CENTRALINOproject/CENTRALINO_BETA/Design/Software/Arduino_sketches/Graphic_&_Oled/coordinate-grid-graph-paper_238032.jpg

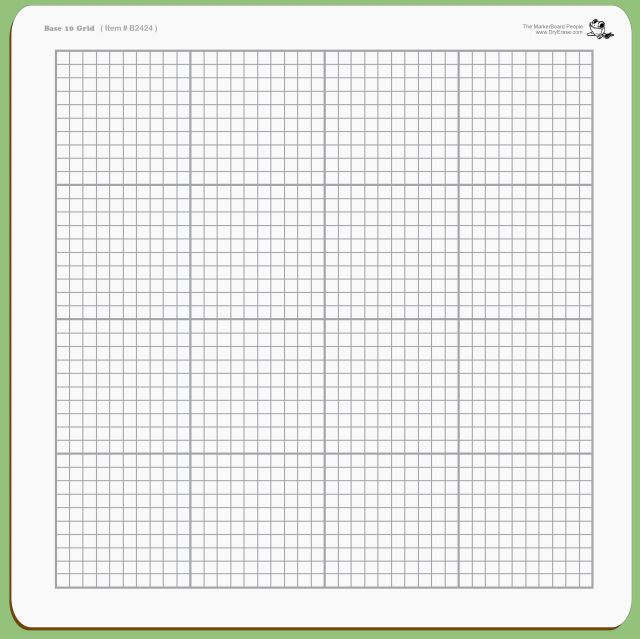
Design/Software/Arduino_sketches/Graphic_&_Oled/coordinate-grid-graph-paper_238032.jpg
