CENTRALINOproject/CENTRALINO_BETA/Design/Software/Arduino_sketches/Graphic_&_Oled/DIYmall-0-96-Inch-Yellow-and-Blue-I2C-IIC-OLED-LCD-Module-Serial-128X64-Display-for.jpg

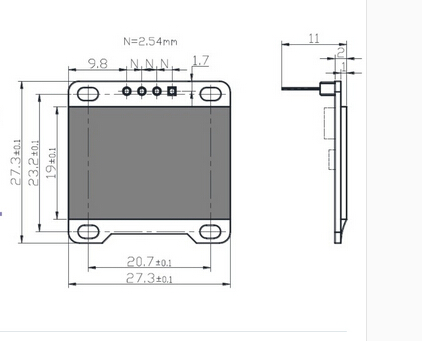
Design/Software/Arduino_sketches/Graphic_&_Oled/DIYmall-0-96-Inch-Yellow-and-Blue-I2C-IIC-OLED-LCD-Module-Serial-128X64-Display-for.jpg
