CENTRALINOproject/CENTRALINO_BETA/Information_Gathering/Multimedia/bluetooth_pinout/HC-05-FC-114-HC-06-FC-114-Connections-to-Arduino.jpg

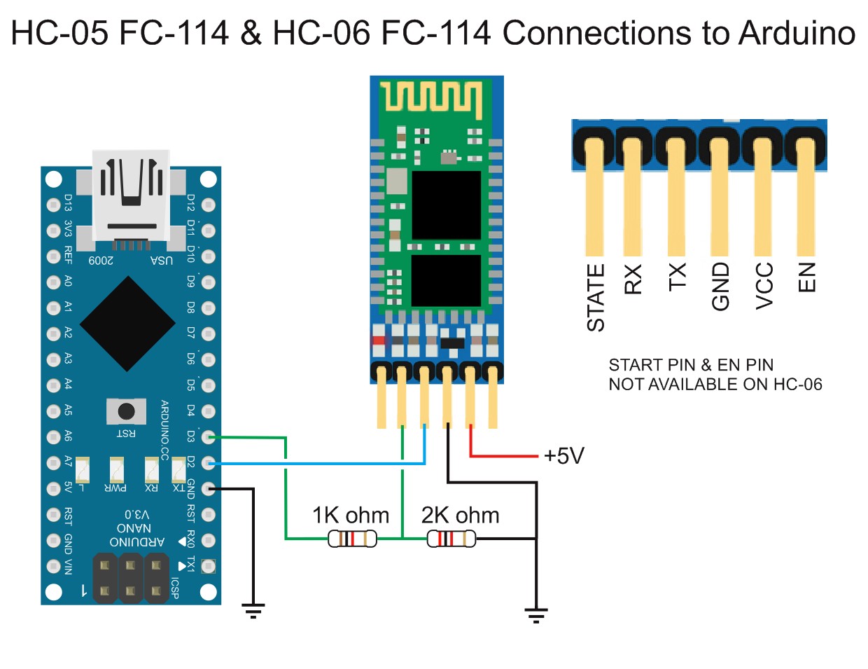
Information_Gathering/Multimedia/bluetooth_pinout/HC-05-FC-114-HC-06-FC-114-Connections-to-Arduino.jpg
