CENTRALINOproject/CENTRALINO_BETA/Information_Gathering/Multimedia/calcolo_per_resistenza.jpg

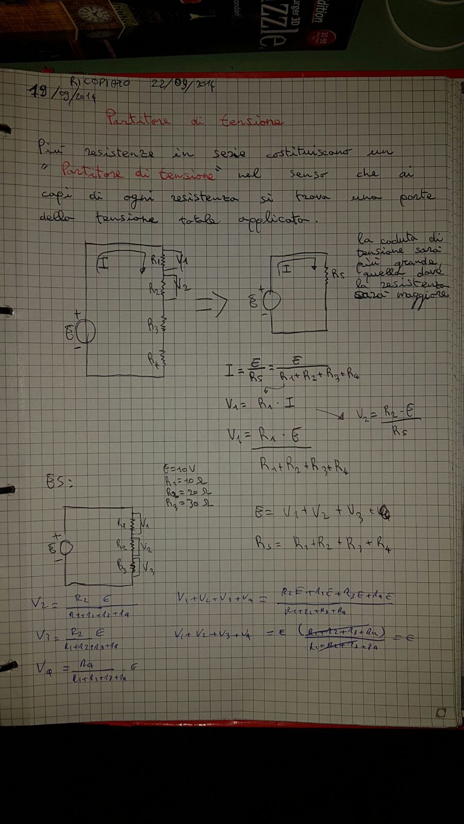
Information_Gathering/Multimedia/calcolo_per_resistenza.jpg
