CENTRALINOproject/CENTRALINO_BETA/Information_Gathering/Multimedia/hc_05_06_multimedia/bluetooth hc05.png

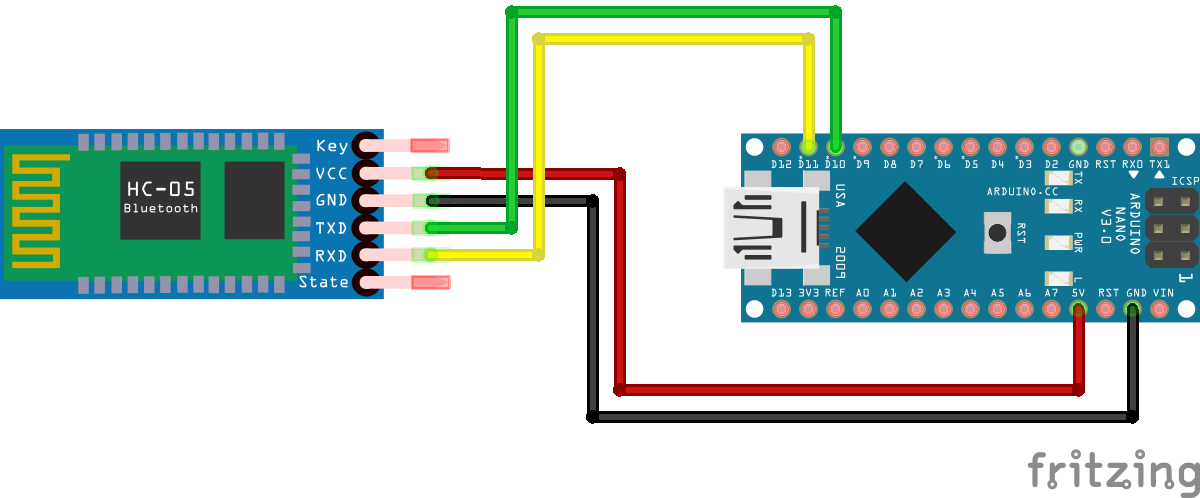
Information_Gathering/Multimedia/hc_05_06_multimedia/bluetooth hc05.png
