CENTRALINOproject/CENTRALINO_BETA/Information_Gathering/Multimedia/hc_05_06_multimedia/hc06_arduino.jpg

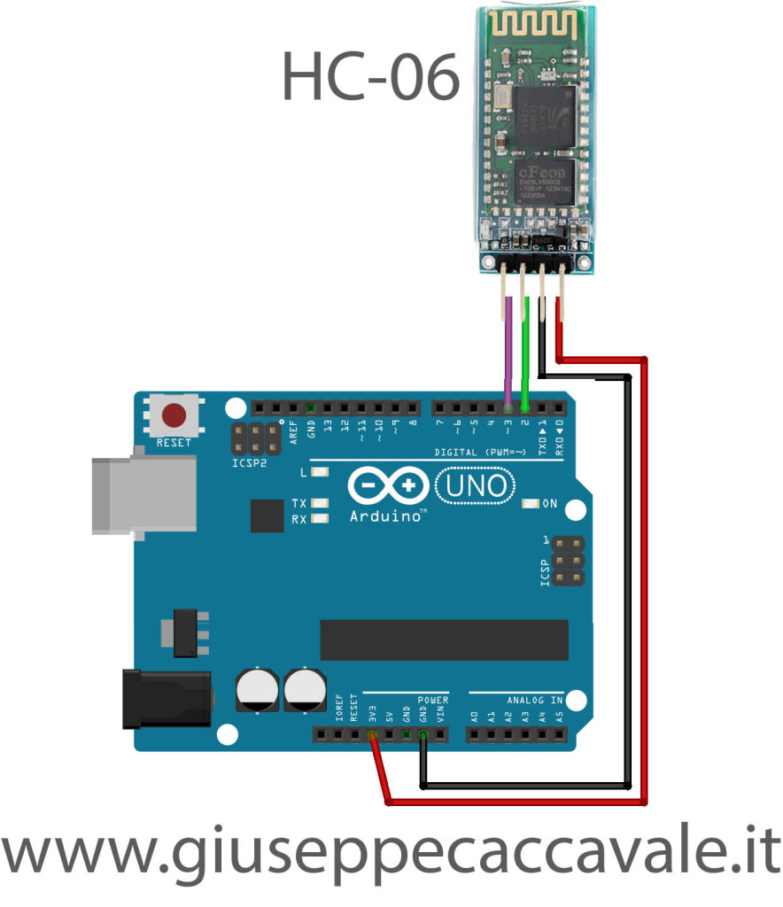
Information_Gathering/Multimedia/hc_05_06_multimedia/hc06_arduino.jpg
