CENTRALINOproject/CENTRALINO_BETA/Information_Gathering/Multimedia/Ir_pinout/ir_receiver_sender_bb.png

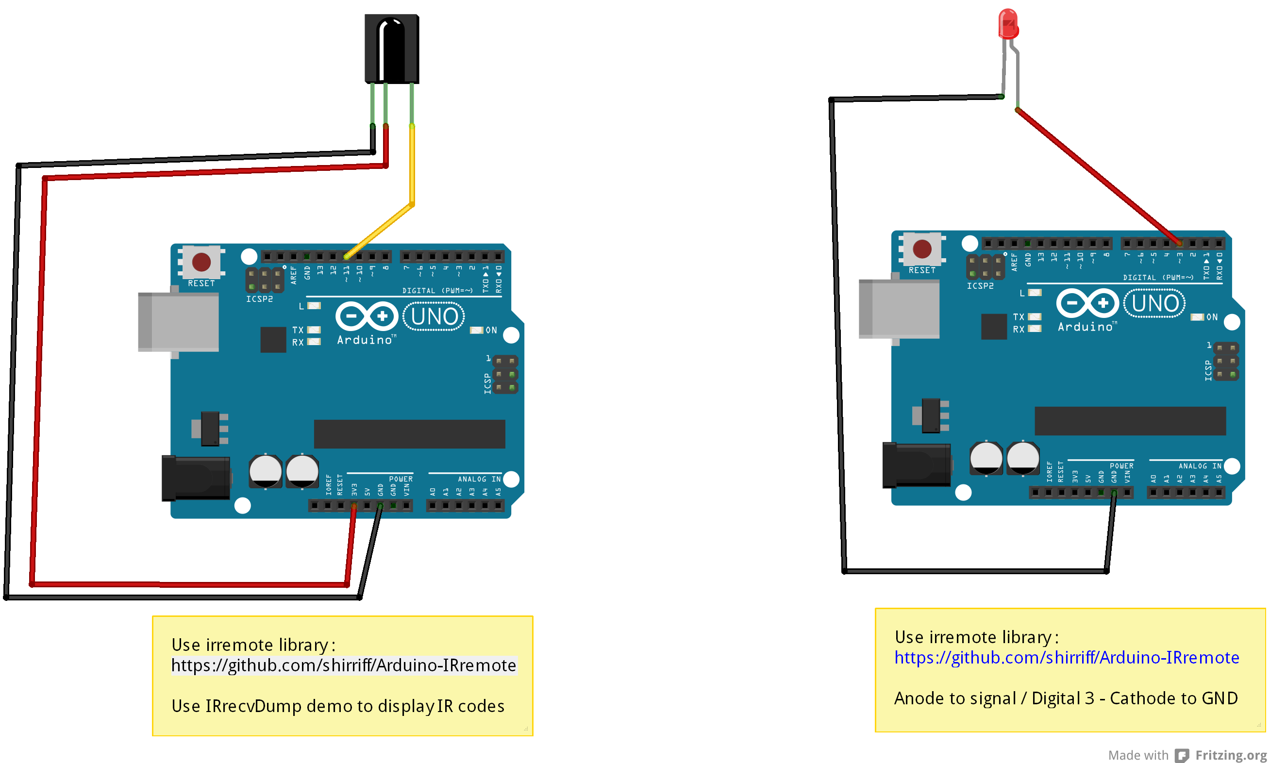
Information_Gathering/Multimedia/Ir_pinout/ir_receiver_sender_bb.png
