CENTRALINOproject/CENTRALINO_BETA/Information_Gathering/Multimedia/mpu6050_multimedia/IMAG0190.jpg

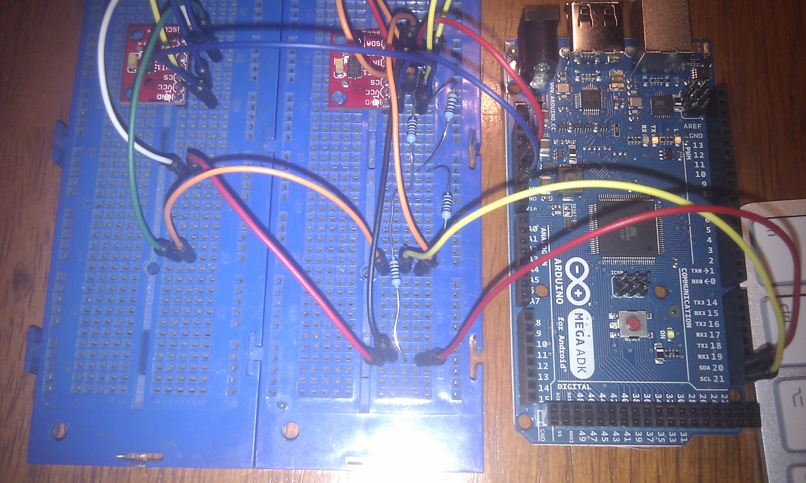
Information_Gathering/Multimedia/mpu6050_multimedia/IMAG0190.jpg
