CENTRALINOproject/CENTRALINO_BETA/Information_Gathering/Multimedia/mpu6050_multimedia/Immagine2.png

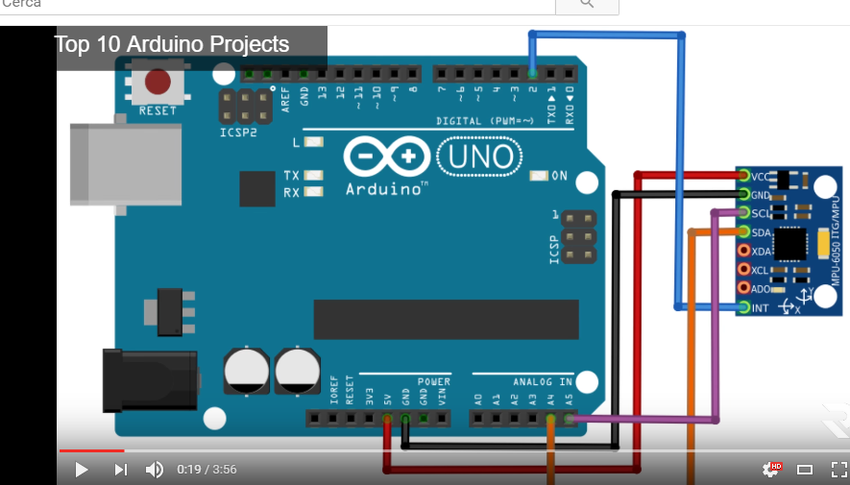
Information_Gathering/Multimedia/mpu6050_multimedia/Immagine2.png
