CENTRALINOproject/CENTRALINO_BETA/Information_Gathering/Multimedia/mpu6050_multimedia/MPU 506 connectivity.jpg

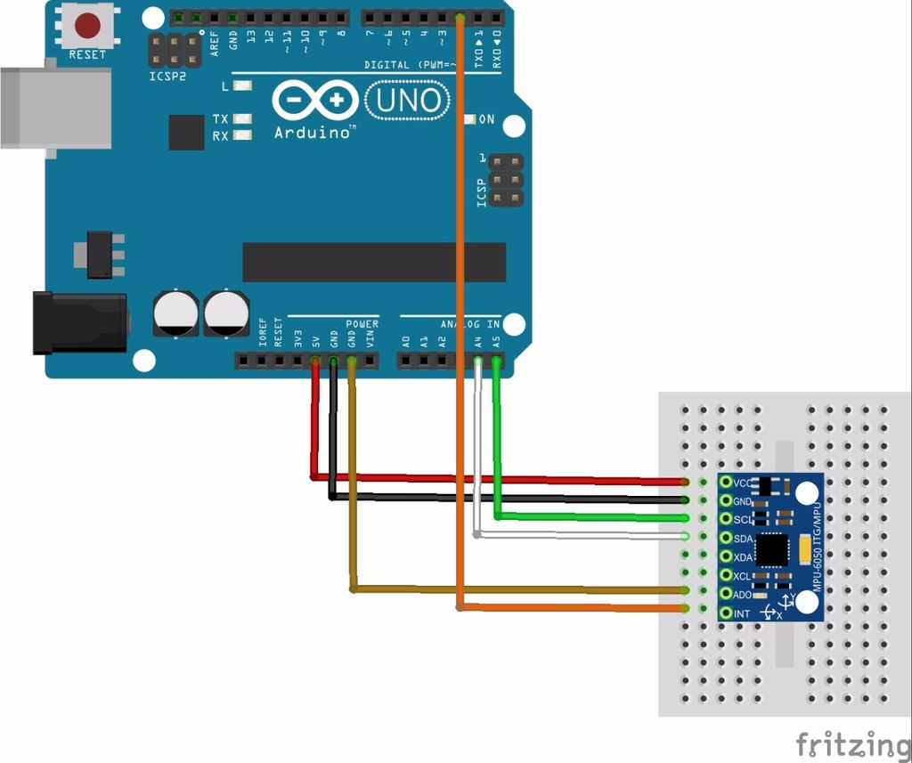
Information_Gathering/Multimedia/mpu6050_multimedia/MPU 506 connectivity.jpg
