CENTRALINOproject/CENTRALINO_BETA/Information_Gathering/Multimedia/mpu6050_multimedia/MPU 5060 skin.jpg

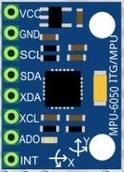
Information_Gathering/Multimedia/mpu6050_multimedia/MPU 5060 skin.jpg
