CENTRALINOproject/CENTRALINO_BETA/Information_Gathering/Multimedia/oled_display/6243.jpg

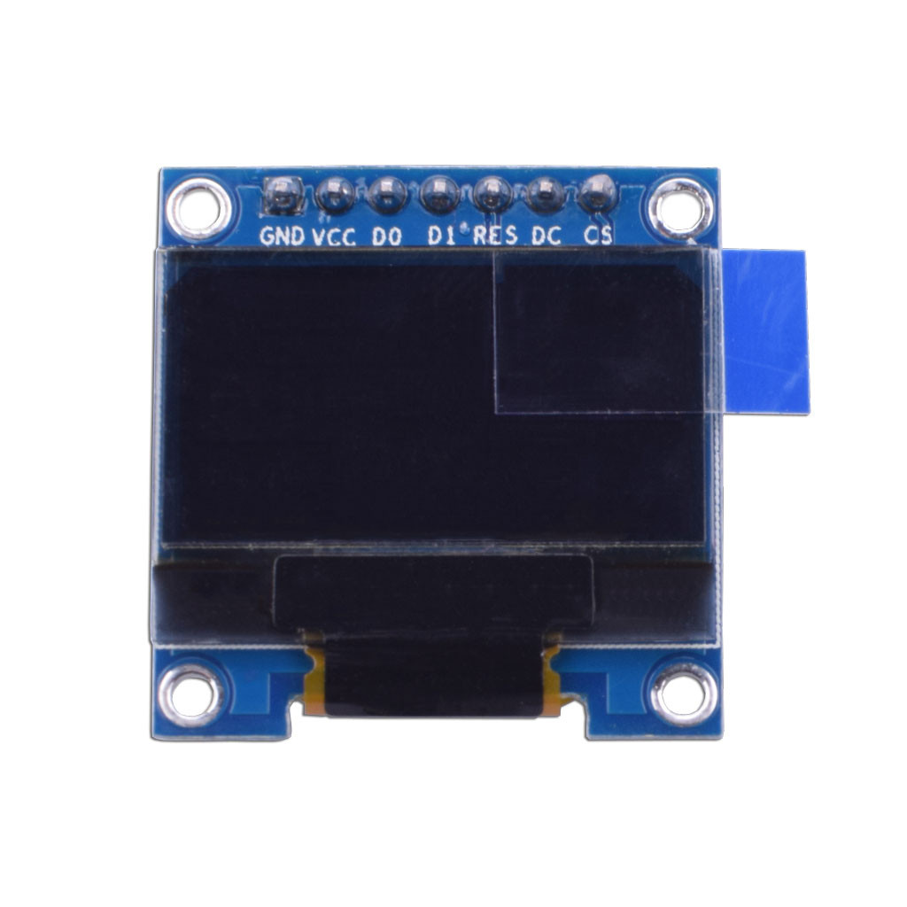
Information_Gathering/Multimedia/oled_display/6243.jpg
