CENTRALINOproject/CENTRALINO_BETA/Information_Gathering/Multimedia/oled_display/17577241452_b7d5964376_o.jpg

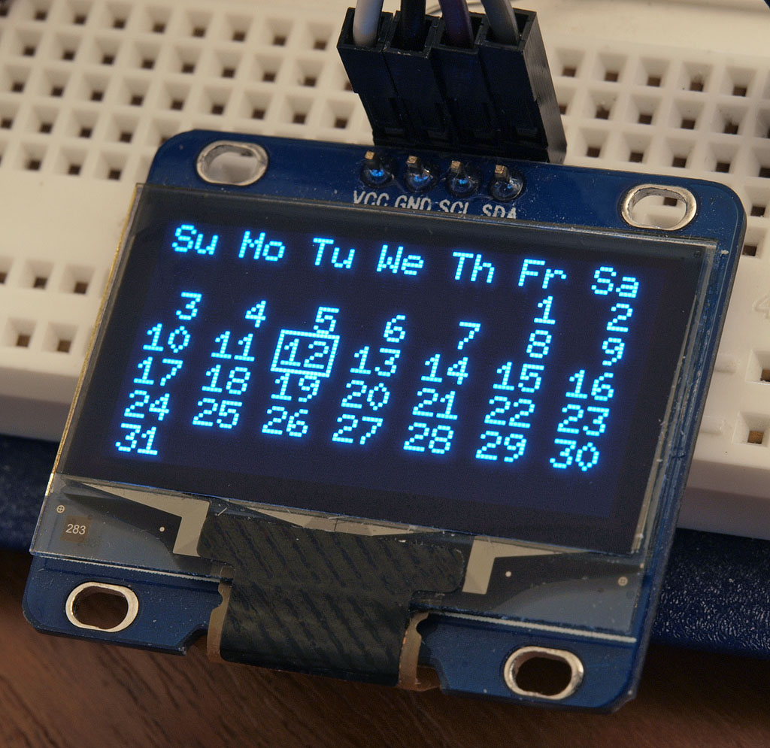
Information_Gathering/Multimedia/oled_display/17577241452_b7d5964376_o.jpg
