CENTRALINOproject/CENTRALINO_BETA/Information_Gathering/Multimedia/oled_display/UT8FCTDXJJaXXagOFbXT.jpg

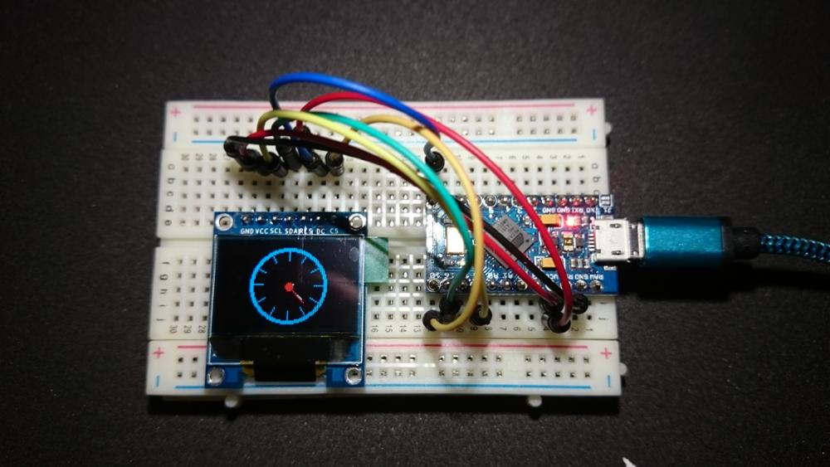
Information_Gathering/Multimedia/oled_display/UT8FCTDXJJaXXagOFbXT.jpg
