CENTRALINOproject/CENTRALINO_BETA/Information_Gathering/Multimedia/various_multimedia/Immagine5.png

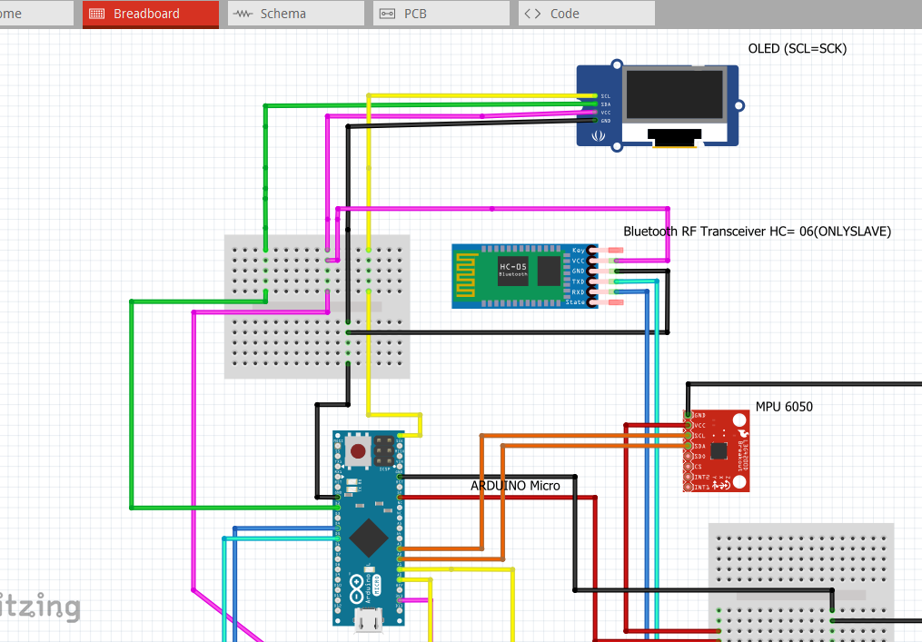
Information_Gathering/Multimedia/various_multimedia/Immagine5.png
