CENTRALINOproject/CENTRALINO_BETA/Project_Report/Appinventor_blocks/cap/Capture1.JPG

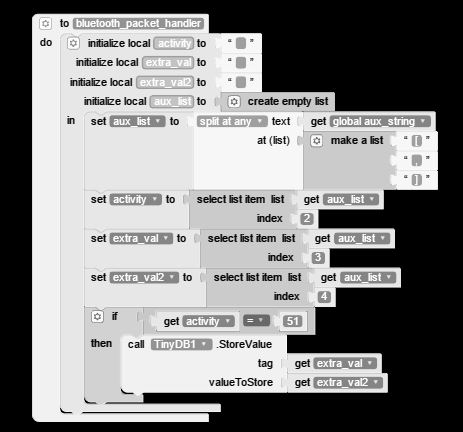
Project_Report/Appinventor_blocks/cap/Capture1.JPG
