CENTRALINOproject/CENTRALINO_BETA/Project_Report/Appinventor_blocks/cap/Capture2.JPG

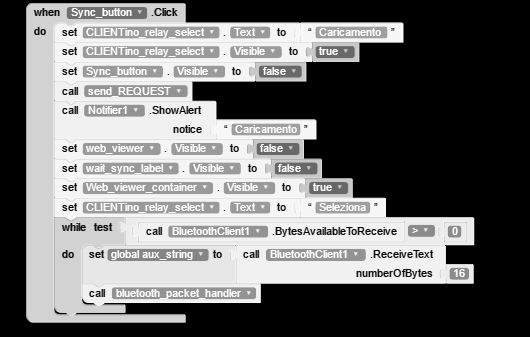
Project_Report/Appinventor_blocks/cap/Capture2.JPG
