CENTRALINOproject/CENTRALINO_BETA/Project_Report/Appinventor_blocks/cap/Capture3.JPG

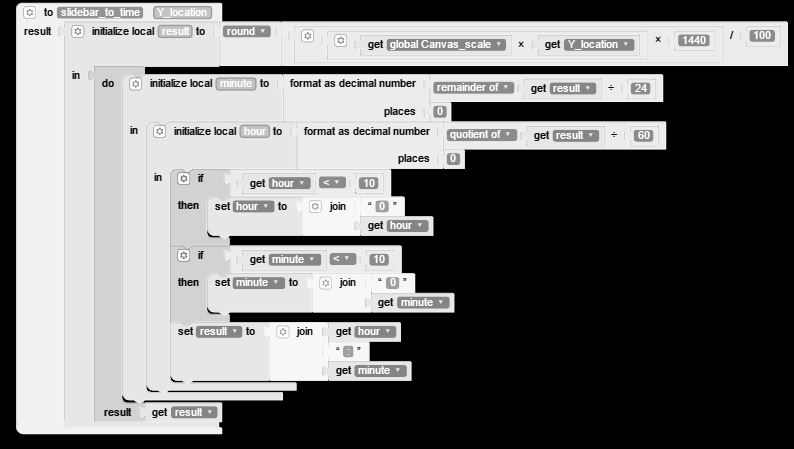
Project_Report/Appinventor_blocks/cap/Capture3.JPG
