CENTRALINOproject/CENTRALINO_BETA/Project_Report/Appinventor_blocks/cap/Capture4.JPG

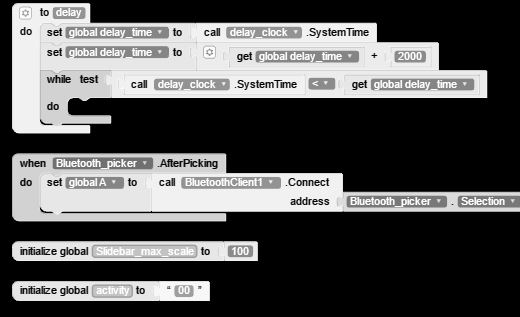
Project_Report/Appinventor_blocks/cap/Capture4.JPG
