CENTRALINOproject/CENTRALINO_BETA/Project_Report/Appinventor_blocks/cap/Capture5.JPG

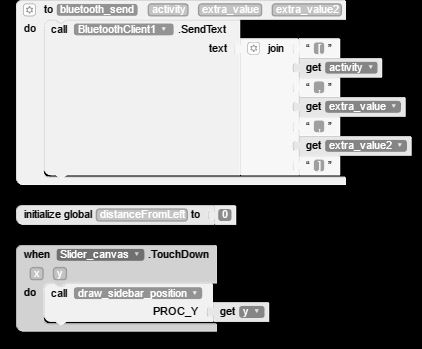
Project_Report/Appinventor_blocks/cap/Capture5.JPG
