CENTRALINOproject/CENTRALINO_BETA/Project_Report/Appinventor_blocks/cap/Capture6.JPG

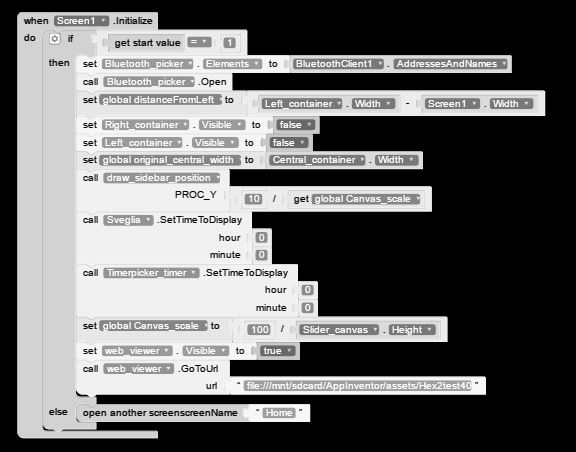
Project_Report/Appinventor_blocks/cap/Capture6.JPG
