CENTRALINOproject/CENTRALINO_BETA/Project_Report/Appinventor_blocks/cap/Capture7.JPG

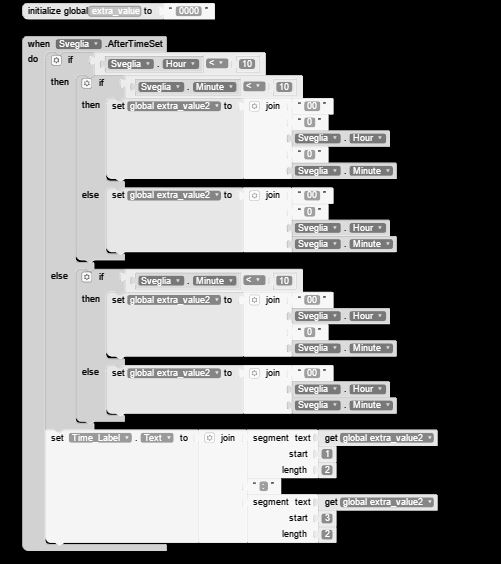
Project_Report/Appinventor_blocks/cap/Capture7.JPG
