CENTRALINOproject/CENTRALINO_BETA/Project_Report/Appinventor_blocks/cap/Capture8.JPG

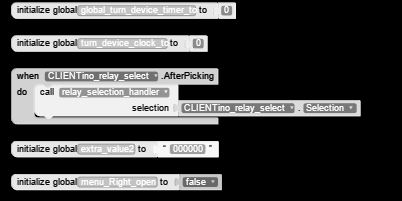
Project_Report/Appinventor_blocks/cap/Capture8.JPG
