CENTRALINOproject/CENTRALINO_BETA/Project_Report/Appinventor_blocks/cap/Capture11.JPG

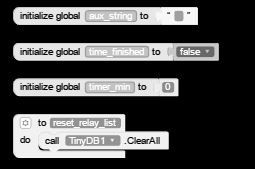
Project_Report/Appinventor_blocks/cap/Capture11.JPG
