CENTRALINOproject/CENTRALINO_BETA/Project_Report/Appinventor_blocks/cap/Capture12.JPG

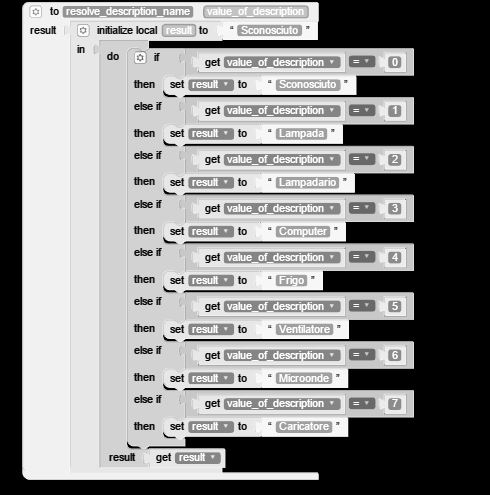
Project_Report/Appinventor_blocks/cap/Capture12.JPG
