CENTRALINOproject/CENTRALINO_BETA/Project_Report/Appinventor_blocks/cap/Capture13.JPG

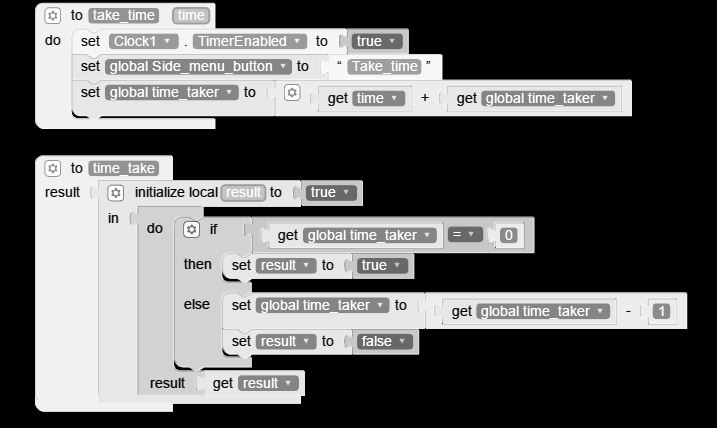
Project_Report/Appinventor_blocks/cap/Capture13.JPG
