CENTRALINOproject/CENTRALINO_BETA/Project_Report/Appinventor_blocks/cap/Capture14.JPG

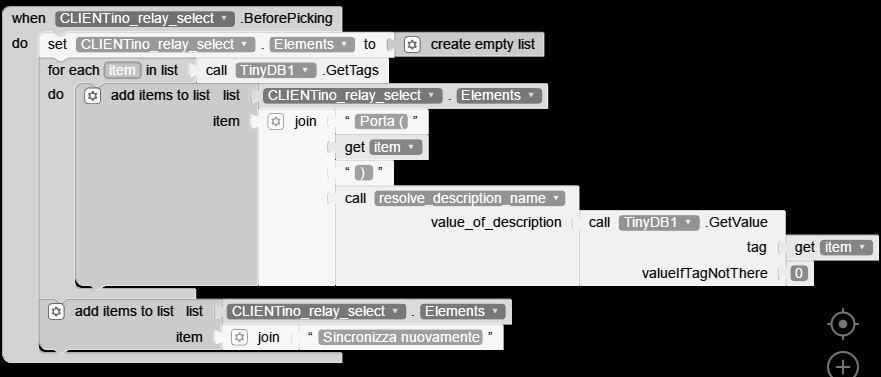
Project_Report/Appinventor_blocks/cap/Capture14.JPG
