CENTRALINOproject/CENTRALINO_BETA/Project_Report/Appinventor_blocks/cap/Capture16.JPG

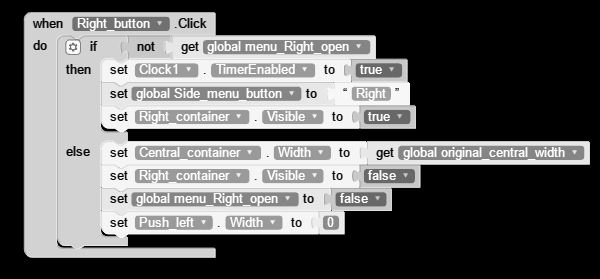
Project_Report/Appinventor_blocks/cap/Capture16.JPG
