CENTRALINOproject/CENTRALINO_BETA/Project_Report/Appinventor_blocks/cap/Capture17.JPG

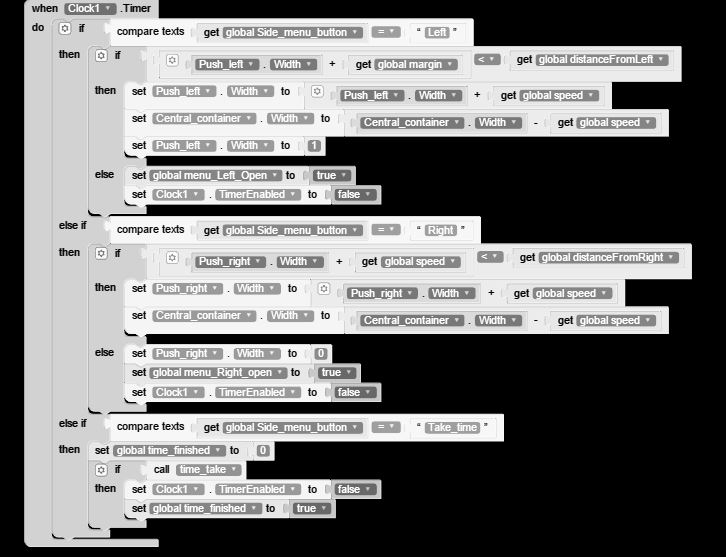
Project_Report/Appinventor_blocks/cap/Capture17.JPG
