CENTRALINOproject/CENTRALINO_BETA/Project_Report/Appinventor_blocks/cap/Capture18.JPG

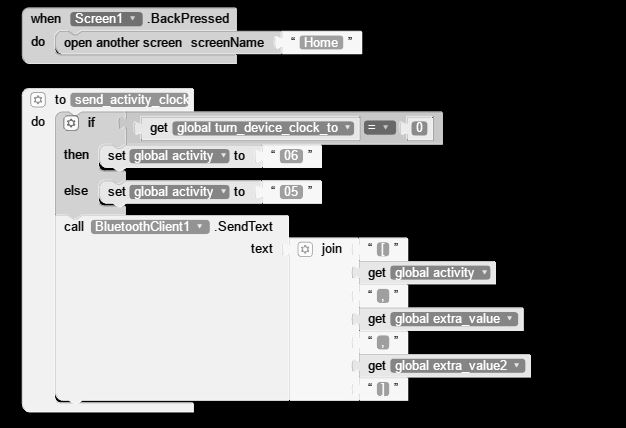
Project_Report/Appinventor_blocks/cap/Capture18.JPG
