CENTRALINOproject/CENTRALINO_BETA/Project_Report/Appinventor_blocks/cap/Capture19.JPG

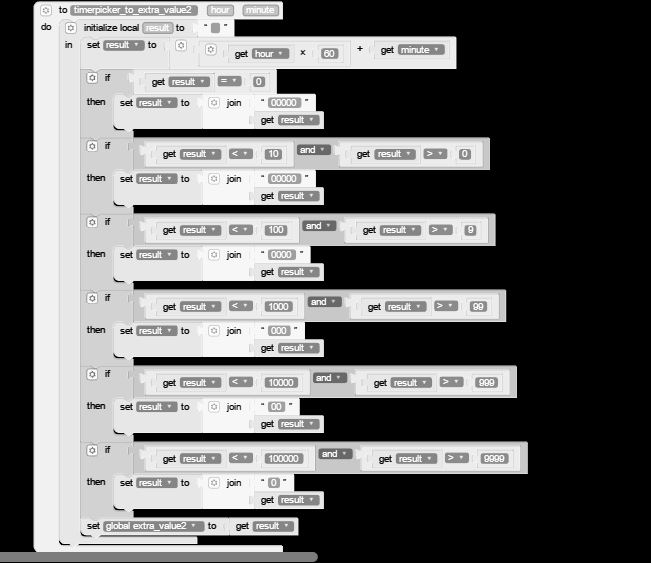
Project_Report/Appinventor_blocks/cap/Capture19.JPG
