CENTRALINOproject/CENTRALINO_BETA/Project_Report/Appinventor_blocks/cap/Capture20.JPG

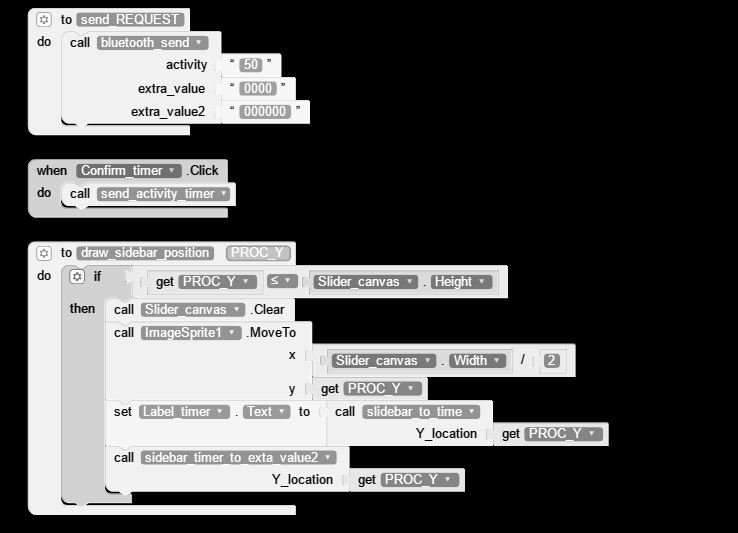
Project_Report/Appinventor_blocks/cap/Capture20.JPG
