CENTRALINOproject/CENTRALINO_BETA/Project_Report/Appinventor_blocks/cap/Capture22.JPG

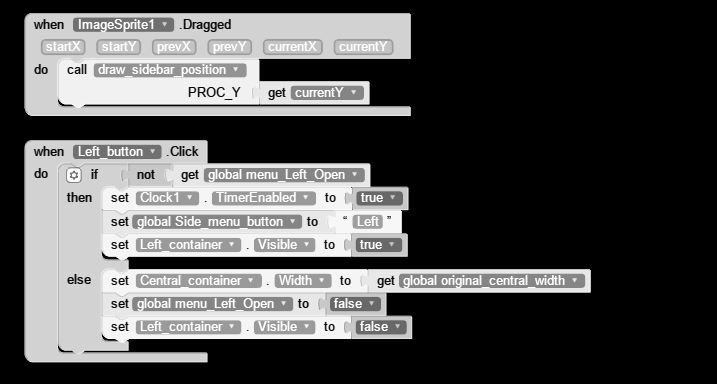
Project_Report/Appinventor_blocks/cap/Capture22.JPG
