CENTRALINOproject/CENTRALINO_BETA/Project_Report/Appinventor_blocks/cap/Capture23.JPG

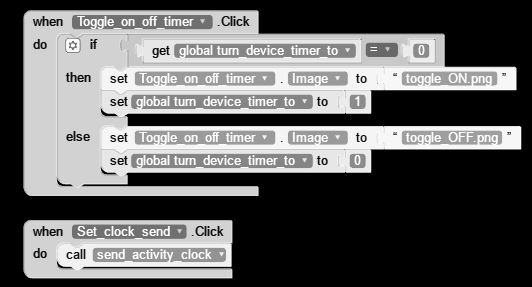
Project_Report/Appinventor_blocks/cap/Capture23.JPG
