CENTRALINOproject/CENTRALINO_BETA/Project_Report/Appinventor_blocks/Capture1.jpg

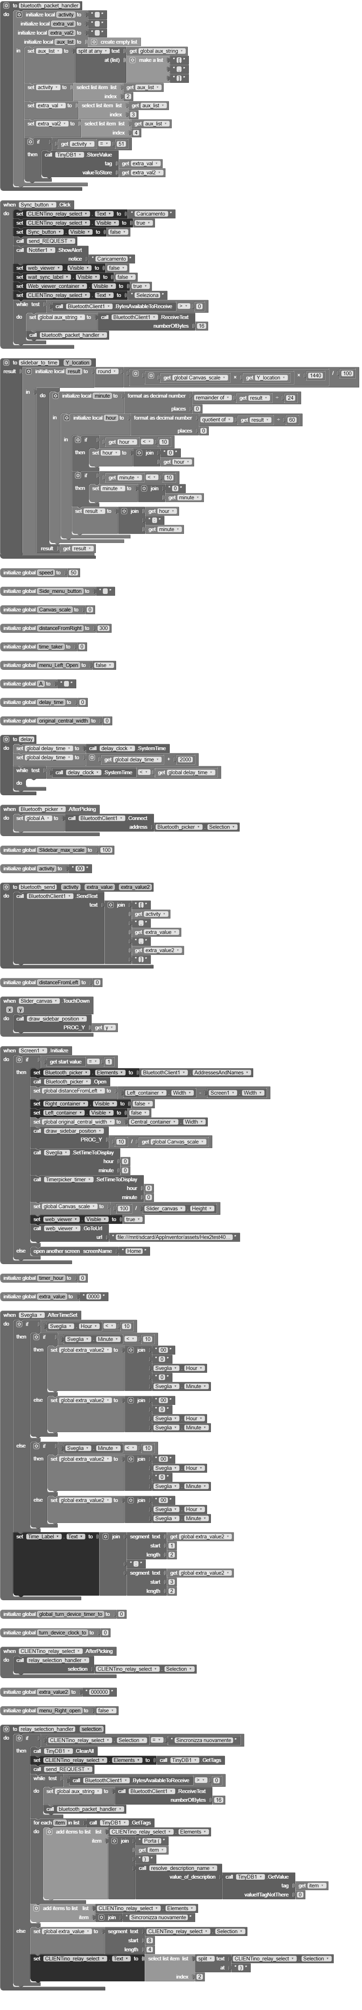
Project_Report/Appinventor_blocks/Capture1.jpg
