CENTRALINOproject/CENTRALINO_BETA/Project_Report/Appinventor_blocks/Capture2.jpg

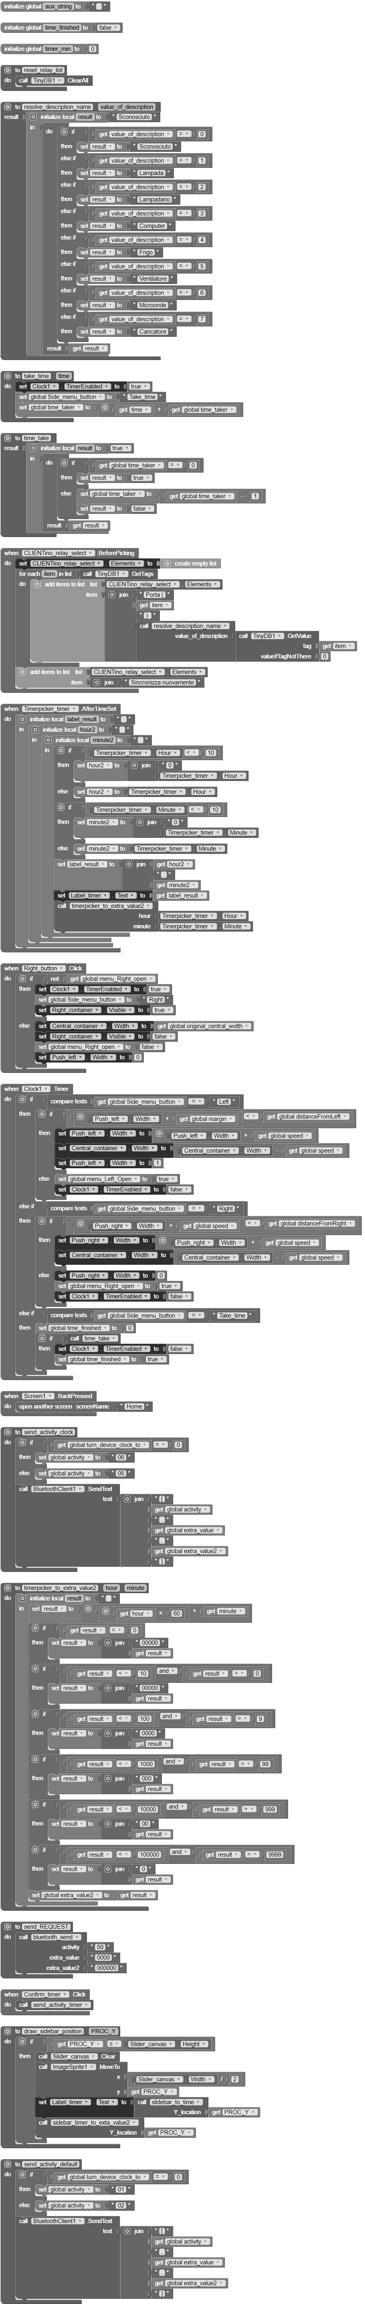
Project_Report/Appinventor_blocks/Capture2.jpg
