CENTRALINOproject/CENTRALINO_BETA/Project_Report/Appinventor_blocks/Capture3.jpg

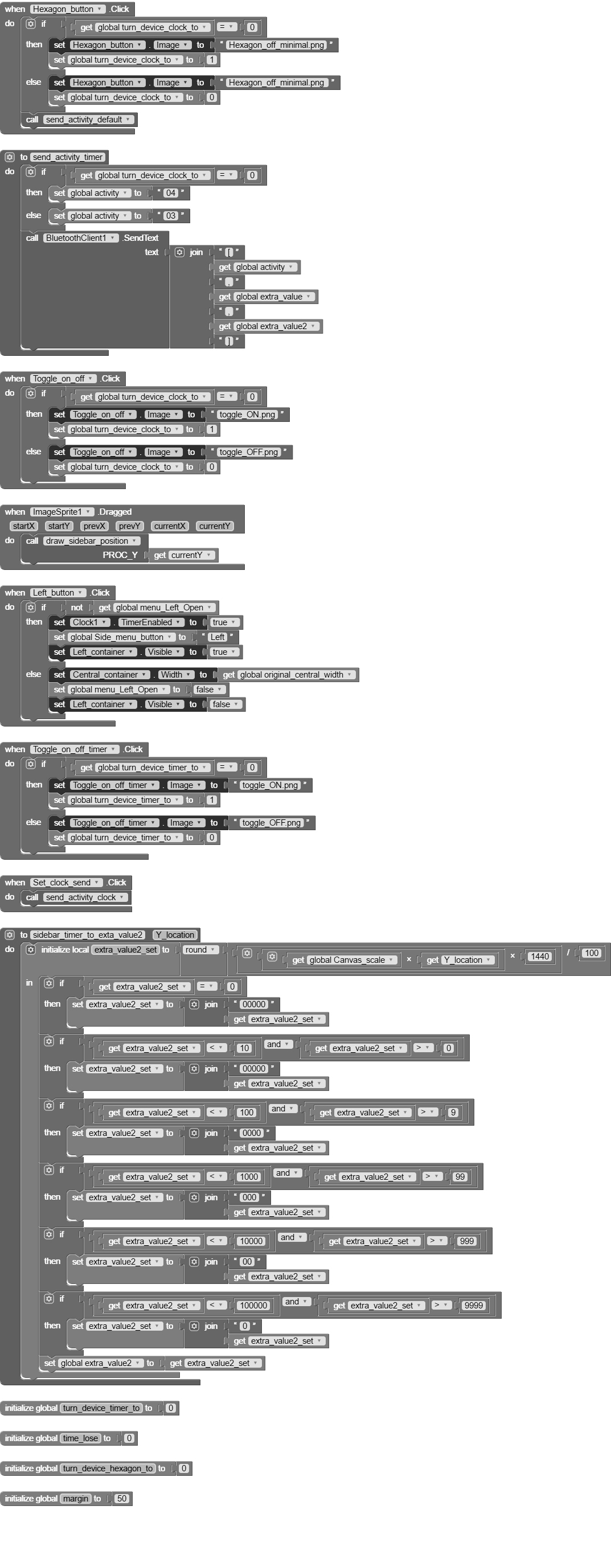
Project_Report/Appinventor_blocks/Capture3.jpg
