CENTRALINOproject/CENTRALINO_BETA/Project_Report/Appinventor_blocks/page 1.jpg

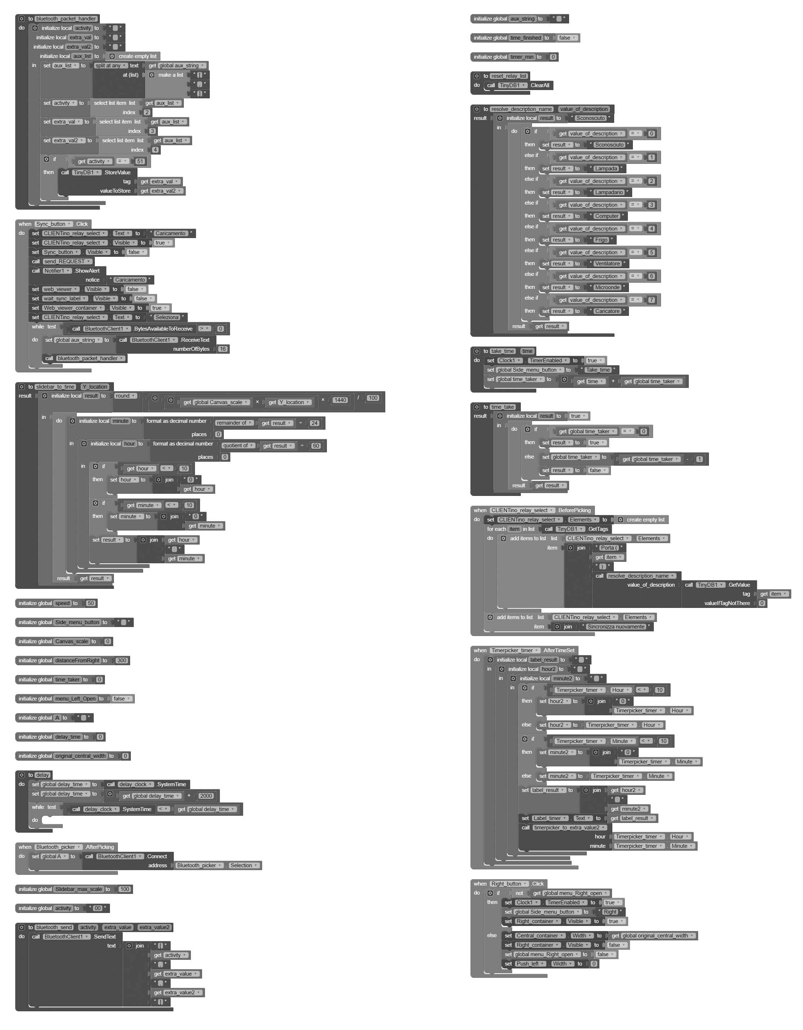
Project_Report/Appinventor_blocks/page 1.jpg
