CENTRALINOproject/CENTRALINO_BETA/Project_Report/Appinventor_blocks/page 2.jpg

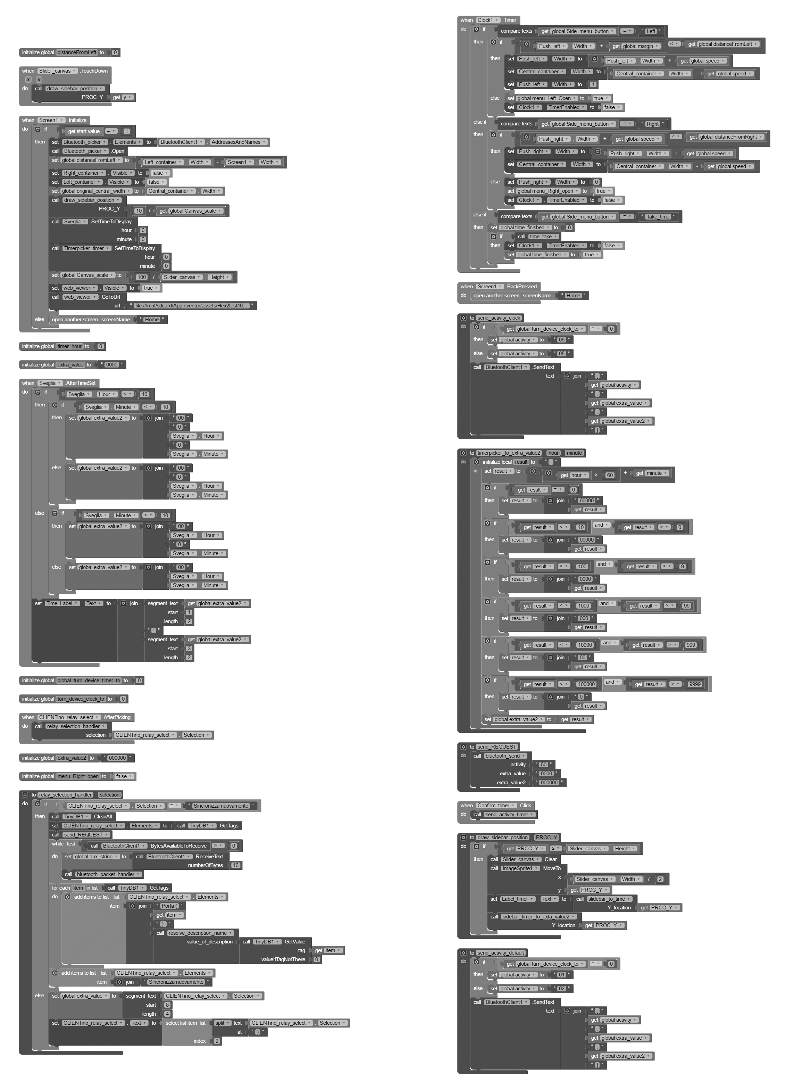
Project_Report/Appinventor_blocks/page 2.jpg
