CENTRALINOproject/CENTRALINO_BETA/Project_Report/Appinventor_blocks/page 3.jpg

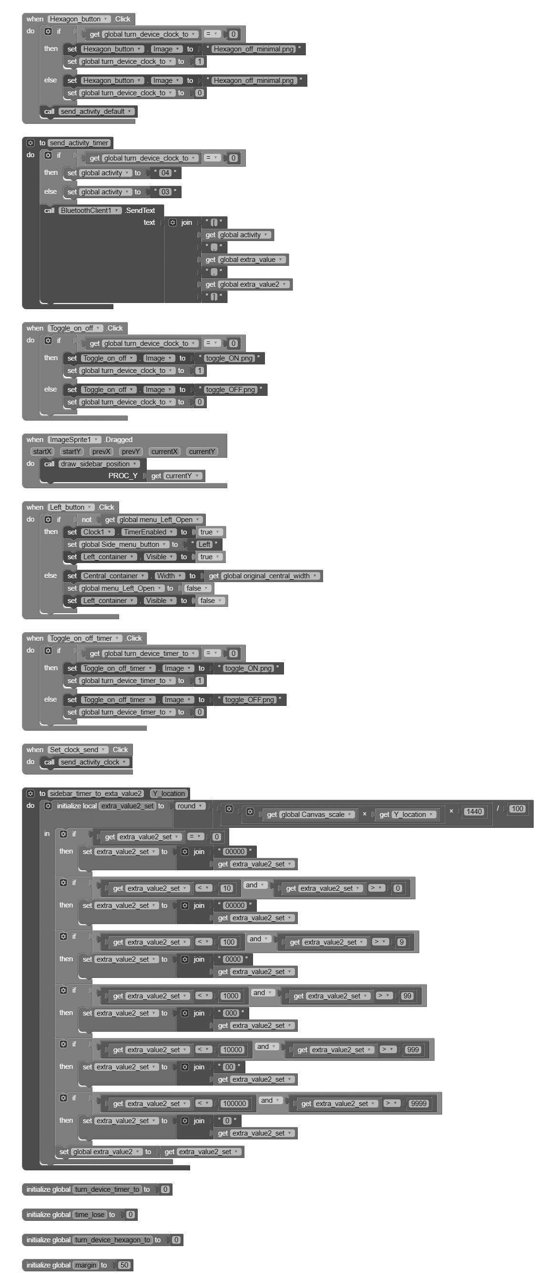
Project_Report/Appinventor_blocks/page 3.jpg
