CENTRALINOproject/CENTRALINO_BETA/Information_Gathering/Multimedia/flex_sensor_multimedia/flex sensor test.png

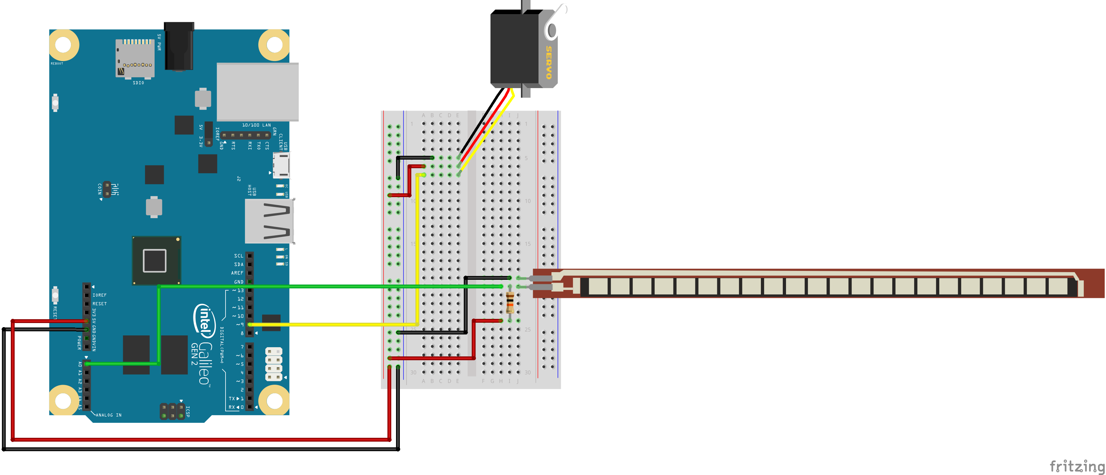
Information_Gathering/Multimedia/flex_sensor_multimedia/flex sensor test.png
