CENTRALINOproject/CENTRALINO_BETA/Design/Software/Arduino_sketches/Graphic_&_Oled/OLED_Analog_Clock/Sinclair_M.c

// Sinclair_M.c
// Font type    : Full (95 characters)
// Font size    : 16x16 pixels
// Memory usage : 3044 bytes

#if defined(__AVR__)
    #include <avr/pgmspace.h>
    #define fontdatatype const uint8_t
#elif defined(__PIC32MX__)
    #define PROGMEM
    #define fontdatatype const unsigned char
#elif defined(__arm__)
    #define PROGMEM
    #define fontdatatype const unsigned char
#endif

fontdatatype Sinclair_M[3044] PROGMEM={
0x10,0x10,0x20,0x5F,
0x00,0x00,0x00,0x00,0x00,0x00,0x00,0x00,0x00,0x00,0x00,0x00,0x00,0x00,0x00,0x00,0x00,0x00,0x00,0x00,0x00,0x00,0x00,0x00,0x00,0x00,0x00,0x00,0x00,0x00,0x00,0x00,  // <space>
0x00,0x00,0x00,0x00,0x00,0x00,0x00,0x00,0xFF,0xFF,0x00,0x00,0x00,0x00,0x00,0x00,0x00,0x00,0x00,0x00,0x00,0x00,0x00,0x00,0x33,0x33,0x00,0x00,0x00,0x00,0x00,0x00,  // !
0x00,0x00,0x00,0x00,0x00,0x00,0x0F,0x0F,0x00,0x00,0x0F,0x0F,0x00,0x00,0x00,0x00,0x00,0x00,0x00,0x00,0x00,0x00,0x00,0x00,0x00,0x00,0x00,0x00,0x00,0x00,0x00,0x00,  // "
0x00,0x00,0x30,0x30,0xFC,0xFC,0x30,0x30,0x30,0x30,0xFC,0xFC,0x30,0x30,0x00,0x00,0x00,0x00,0x0C,0x0C,0x3F,0x3F,0x0C,0x0C,0x0C,0x0C,0x3F,0x3F,0x0C,0x0C,0x00,0x00,  // #
0x00,0x00,0xFC,0xFC,0xCC,0xCC,0xFF,0xFF,0xCC,0xCC,0xCC,0xCC,0x00,0x00,0x00,0x00,0x00,0x00,0x0C,0x0C,0x0C,0x0C,0x3F,0x3F,0x0C,0x0C,0x0F,0x0F,0x00,0x00,0x00,0x00,  // $
0x00,0x00,0x3C,0x3C,0x3C,0x3C,0x00,0x00,0xC0,0xC0,0x30,0x30,0x0C,0x0C,0x00,0x00,0x00,0x00,0x30,0x30,0x0C,0x0C,0x03,0x03,0x00,0x00,0x3C,0x3C,0x3C,0x3C,0x00,0x00,  // %
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
0x00,0x00,0x00,0x00,0x30,0x30,0x0C,0x0C,0x30,0x30,0x0C,0x0C,0x00,0x00,0x00,0x00,0x00,0x00,0x00,0x00,0x00,0x00,0x00,0x00,0x00,0x00,0x00,0x00,0x00,0x00,0x00,0x00,  // ~
};
